weberel/tide-clock/simulator/tide_display.png

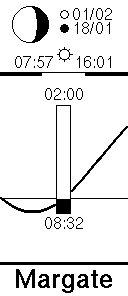
simulator/tide_display.png
