weberel/tide-clock/firmware/revB/src/astro.c

/**
 * Astronomical Calculations
 *
 * Moon phase: Jean Meeus algorithm (Astronomical Algorithms Ch.49)
 * Sunrise/Sunset: NOAA Solar Calculator
 * Location loaded from location_config.h
 */

#include "astro.h"
#include "location_config.h"
#include <math.h>

#ifndef M_PI
#define M_PI 3.14159265358979323846
#endif

// Calculate day of year (1-366) from year, month, day
static int calc_day_of_year(int year, int month, int day) {
    static const int days_before_month[] = {0, 31, 59, 90, 120, 151, 181, 212, 243, 273, 304, 334};
    int doy = days_before_month[month - 1] + day;
    // Add leap day if past February in a leap year
    int is_leap = (year % 4 == 0 && (year % 100 != 0 || year % 400 == 0));
    if (is_leap && month > 2) {
        doy++;
    }
    return doy;
}

// ============================================================================
// Moon Phase Calculations (Meeus Algorithm)
// ============================================================================

/**
 * Calculate exact time of a moon phase.
 * @param k Lunation number (k=0 is Jan 6, 2000 new moon)
 * @return Julian Ephemeris Day of the phase
 */
static double moon_phase_jde(double k) {
    double T = k / 1236.85;
    double T2 = T * T;
    double T3 = T2 * T;
    double T4 = T3 * T;

    double JDE = 2451550.09766 + 29.530588861*k
                 + 0.00015437*T2 - 0.000000150*T3 + 0.00000000073*T4;

    double M = fmod(2.5534 + 29.10535670*k - 0.0000014*T2, 360.0) * M_PI / 180.0;
    double Mp = fmod(201.5643 + 385.81693528*k + 0.0107582*T2, 360.0) * M_PI / 180.0;
    double F = fmod(160.7108 + 390.67050284*k - 0.0016118*T2, 360.0) * M_PI / 180.0;
    double Om = fmod(124.7746 - 1.56375588*k + 0.0020672*T2, 360.0) * M_PI / 180.0;
    double E = 1 - 0.002516*T - 0.0000074*T2;

    double corr = -0.40720*sin(Mp) + 0.17241*E*sin(M) + 0.01608*sin(2*Mp)
                + 0.01039*sin(2*F) + 0.00739*E*sin(Mp-M) - 0.00514*E*sin(Mp+M)
                + 0.00208*E*E*sin(2*M) - 0.00111*sin(Mp-2*F) - 0.00057*sin(Mp+2*F)
                + 0.00056*E*sin(2*Mp+M) - 0.00042*sin(3*Mp) + 0.00042*E*sin(M+2*F)
                + 0.00038*E*sin(M-2*F) - 0.00024*E*sin(2*Mp-M) - 0.00017*sin(Om);

    return JDE + corr;
}

static time64_t jde_to_time64(double JDE) {
    return (time64_t)((JDE - 2440587.5) * 86400.0);
}

float calculate_moon_phase(time64_t dt) {
    struct tm tm;
    time_to_tm(dt, &tm);
    int year = tm.tm_year + 1900;
    int month = tm.tm_mon + 1;
    int day = tm.tm_mday;
    double hour = tm.tm_hour + tm.tm_min/60.0;

    if (month <= 2) { year--; month += 12; }
    int A = year / 100;
    int B = 2 - A + A/4;
    double JD = (int)(365.25 * (year + 4716)) + (int)(30.6001 * (month + 1))
                + day + hour/24.0 + B - 1524.5;

    double T = (JD - 2451545.0) / 36525.0;
    double D = fmod(297.8501921 + 445267.1114034*T, 360.0);
    double M = fmod(357.5291092 + 35999.0502909*T, 360.0) * M_PI/180;
    double Mp = fmod(134.9633964 + 477198.8675055*T, 360.0) * M_PI/180;

    double i = 180.0 - D - 6.289*sin(Mp) + 2.100*sin(M) - 1.274*sin(2*D*M_PI/180 - Mp);
    i = fmod(i, 360.0);
    if (i < 0) i += 360.0;

    // Convert to 0=new, 0.5=full convention
    double phase = 0.5 - (i / 360.0);
    if (phase < 0) phase += 1.0;
    return (float)phase;
}

void find_next_full_new_moon(time64_t dt, time64_t *next_full, time64_t *next_new) {
    struct tm tm;
    time_to_tm(dt, &tm);
    int y = tm.tm_year + 1900;
    int m = tm.tm_mon + 1;
    int d = tm.tm_mday;
    int doy = calc_day_of_year(y, m, d);
    double year = y + (doy - 1) / 365.25;
    double k_approx = (year - 2000.0) * 12.3685;
    int k_base = (int)floor(k_approx);

    *next_full = 0;
    *next_new = 0;

    // Find moon phases that are at least tomorrow (not today)
    // This avoids showing "today" as "next" when the event just happened
    time64_t tomorrow_start = dt + 86400 - (tm.tm_hour * 3600 + tm.tm_min * 60 + tm.tm_sec);

    for (int i = -1; i <= 3; i++) {
        int k = k_base + i;
        time64_t t_new = jde_to_time64(moon_phase_jde((double)k));
        if (*next_new == 0 && t_new >= tomorrow_start) *next_new = t_new;

        time64_t t_full = jde_to_time64(moon_phase_jde(k + 0.5));
        if (*next_full == 0 && t_full >= tomorrow_start) *next_full = t_full;
    }
}

// ============================================================================
// Sunrise/Sunset Calculations (NOAA Algorithm)
// ============================================================================

void calculate_sunrise_sunset(time64_t dt, int *sunrise_hour, int *sunrise_min,
                              int *sunset_hour, int *sunset_min) {
    struct tm tm_info;
    time_to_tm(dt, &tm_info);
    int day_of_year = calc_day_of_year(tm_info.tm_year + 1900, tm_info.tm_mon + 1, tm_info.tm_mday);

    float gamma = 2 * M_PI / 365 * (day_of_year - 1);

    float eqtime = 229.18 * (0.000075 + 0.001868 * cos(gamma) - 0.032077 * sin(gamma)
                   - 0.014615 * cos(2*gamma) - 0.040849 * sin(2*gamma));

    float decl = 0.006918 - 0.399912 * cos(gamma) + 0.070257 * sin(gamma)
                 - 0.006758 * cos(2*gamma) + 0.000907 * sin(2*gamma)
                 - 0.002697 * cos(3*gamma) + 0.00148 * sin(3*gamma);

    float lat_rad = LOCATION_LAT * M_PI / 180.0;
    float zenith = 90.833 * M_PI / 180.0;
    float cos_hour_angle = (cos(zenith) / (cos(lat_rad) * cos(decl))) - tan(lat_rad) * tan(decl);
    cos_hour_angle = fmax(-1, fmin(1, cos_hour_angle));

    float hour_angle = acos(cos_hour_angle) * 180.0 / M_PI;

    float sunrise_utc_min = 720 - 4 * (LOCATION_LON + hour_angle) - eqtime;
    float sunset_utc_min = 720 - 4 * (LOCATION_LON - hour_angle) - eqtime;

    float sunrise_utc = sunrise_utc_min / 60.0;
    float sunset_utc = sunset_utc_min / 60.0;

    // Add timezone offset (hours)
    int offset_seconds = get_utc_offset(dt);
    float offset_hours = offset_seconds / 3600.0f;
    float sunrise_local = sunrise_utc + offset_hours;
    float sunset_local = sunset_utc + offset_hours;

    // Handle day wraparound
    if (sunrise_local < 0) sunrise_local += 24.0f;
    if (sunrise_local >= 24) sunrise_local -= 24.0f;
    if (sunset_local < 0) sunset_local += 24.0f;
    if (sunset_local >= 24) sunset_local -= 24.0f;

    *sunrise_hour = (int)sunrise_local;
    *sunrise_min = (int)((sunrise_local - *sunrise_hour) * 60);
    *sunset_hour = (int)sunset_local;
    *sunset_min = (int)((sunset_local - *sunset_hour) * 60);
}
